NanoCodeBug/pawpet-arduino/src/graphics/sprites.h

#pragma once
// <name> = width, height, alpha, encoding, tile_count, <tile offsets...>, image byte array

// tile dimensions: 16x8
// alpha channel: False
// encoding: pack
// total tiles: 5
// byte count: 104
const uint32_t battery[] = {0x00080010,0x00000000,0x00000005,0x00040000,0x000c0008,0x00000010,0xbffdc001,0xbbbdafed,0xbffdbc7d,0xffffc001,0x836dc001,0x836d836d,0x836d836d,0xffffc001,0x806dc001,0x806d806d,0x806d806d,0xffffc001,0x800dc001,0x800d800d,0x800d800d,0xffffc001,0x8001c001,0x90118821,0x800187c1,0xffffc001};

// tile dimensions: 8x8
// alpha channel: False
// encoding: pack
// total tiles: 32
// byte count: 332
const uint32_t icons[] = {0x00080008,0x00000000,0x00000020,0x00020000,0x00060004,0x000a0008,0x000e000c,0x00120010,0x00160014,0x001a0018,0x001e001c,0x00220020,0x00260024,0x002a0028,0x002e002c,0x00320030,0x00360034,0x003a0038,0x003e003c,0xffff6600,0x183c7eff,0x38381000,0x387c7c7c,0x006c6c00,0x60f0f666,0xfe383800,0x3838fefe,0x7c381000,0x000000fe,0x10000000,0x00fe7c38,0x00000000,0x00000000,0x00000000,0x00000000,0x5ac33c00,0x3cc34acb,0x5ac33c00,0xffc35acb,0x24240000,0x00182400,0xffffff00,0x00ffffff,0x0e060200,0x02060e1e,0x38180800,0x08183878,0x00000000,0x00000000,0x00000000,0x00000000,0x818181ff,0xff818181,0x42427e00,0x007e4242,0xbdbd81ff,0xff81bdbd,0x5a427e00,0x007e425a,0xe0e07030,0x387cfef6,0x00000000,0x00000000,0x00000000,0x00000000,0x00000000,0x00000000,0x3c3c0000,0x00003c3c,0x34180000,0x0000183c,0x7a341800,0x00183c7e,0xfffb763c,0x3c7effff,0x00000000,0x00000000,0x00000000,0x00000000,0x00000000,0x00000000,0x00000000,0x00000000};

// tile dimensions: 64x64
// alpha channel: False
// encoding: span
// total tiles: 5
// byte count: 1704
const uint32_t pet_sit[] = {0x00400040,0x00010000,0x00000005,0x00530000,0x010200ac,0x00000153,0x85207f7f,0x89378839,0x86058936,0x8a04892b,0x8b048928,0x8c038927,0x8c028a27,0x8c018b27,0x82018828,0x86288b01,0x8b028103,0x90028429,0x8401902a,0x8301922a,0x8201932a,0x832c942a,0x86038503,0x8301822c,0x82028301,0x822b8501,0x82018401,0x85018501,0x8501822a,0x85018101,0x822a8501,0x81018501,0x84018501,0x8501822b,0x85018101,0x86138401,0x84018212,0x85018201,0x89108401,0x84018212,0x85018201,0x8b0e8401,0x82018312,0x84018301,0x8c0e8401,0x85028412,0x84028101,0x8c168a0d,0x890c8601,0x890c9119,0x880a911b,0x880a8f1e,0x87098e21,0x87088a26,0x88068b27,0x88048c27,0x87048c28,0x88038c29,0x88018429,0x842a8702,0x85299101,0x83018c01,0x8d01852a,0x852b8101,0x852c8e01,0x852b8f01,0x862a8f01,0x85299001,0x86028901,0x88018529,0x86288801,0x89018701,0x86018727,0x87278a01,0x8a018601,0x87018826,0x87268901,0x89018801,0x88018825,0x88258901,0x8a018701,0x87018725,0x87268a01,0x8b018601,0x88028427,0x892d8901,0x87308701,0x84348601,0x00588303,0x85207f7f,0x89378839,0x86058936,0x8a04892b,0x8b048928,0x8c038927,0x8c028a27,0x8c018b27,0x82018828,0x86288b01,0x8b028103,0x90028429,0x901c810d,0x830d8401,0x8301921a,0x9319840d,0x840d8201,0x840f9419,0x85038319,0x840f8603,0x83018219,0x83018301,0x850e8501,0x84018218,0x85018201,0x850d8501,0x85018218,0x85018101,0x850d8501,0x85018218,0x85018101,0x850e8401,0x85018218,0x85018101,0x850e8401,0x84018218,0x85018201,0x850d8401,0x84018219,0x85018201,0x850d8401,0x82018319,0x84018301,0x860d8401,0x8502841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
