NanoCodeBug/pawpet-arduino/simulator/fork/Print.h

/*
  Copyright (c) 2014 Arduino.  All right reserved.

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
  You should have received a copy of the GNU Lesser General Public
  License along with this library; if not, write to the Free Software
  Foundation, Inc., 51 Franklin St, Fifth Floor, Boston, MA  02110-1301  USA
*/

#ifndef Print_h
#define Print_h

#include <inttypes.h>
#include <stdio.h> // for size_t
#include <stdarg.h> // for printf
#define PRINTF_BUF 80

#include <string.h>
#include "Printable.h"

#define DEC 10
#define HEX 16
#define OCT 8
#define BIN 2

class Print
{
  private:
    int write_error;
    size_t printNumber(unsigned long, uint8_t);
    size_t printULLNumber(unsigned long long, uint8_t);
    size_t printFloat(double, uint8_t);
  protected:
    void setWriteError(int err = 1) { write_error = err; }
  public:
    Print() : write_error(0) {}

    int getWriteError() { return write_error; }
    void clearWriteError() { setWriteError(0); }

    virtual size_t write(uint8_t) = 0;
    size_t write(const char *str) {
      if (str == NULL) return 0;
      return write((const uint8_t *)str, strlen(str));
    }
    virtual size_t write(const uint8_t *buffer, size_t size);
    size_t write(const char *buffer, size_t size) {
      return write((const uint8_t *)buffer, size);
    }

    // default to zero, meaning "a single write may block"
    // should be overriden by subclasses with buffering
    virtual int availableForWrite() { return 0; }

    size_t print(const char[]);
    size_t print(char);
    size_t print(unsigned char, int = DEC);
    size_t print(int, int = DEC);
    size_t print(unsigned int, int = DEC);
    size_t print(long, int = DEC);
    size_t print(unsigned long, int = DEC);
    size_t print(long long, int = DEC);
    size_t print(unsigned long long, int = DEC);
    size_t print(double, int = 2);
    size_t print(const Printable&);

    size_t println(const char[]);
    size_t println(char);
    size_t println(unsigned char, int = DEC);
    size_t println(int, int = DEC);
    size_t println(unsigned int, int = DEC);
    size_t println(long, int = DEC);
    size_t println(unsigned long, int = DEC);
    size_t println(long long, int = DEC);
    size_t println(unsigned long long, int = DEC);
    size_t println(double, int = 2);
    size_t println(const Printable&);
    size_t println(void);
    
    void printf(const char[], ...);

    virtual void flush() { /* Empty implementation for backward compatibility */ }
};

#endif
